CarbonComputers/Hackberry-Pi-CM5/RTC-Battery/README.md

# RTC_Battery on HackberryPi_CM5

There is an RTC battery on board on HackberryPi_CM5 and is pre-installed before delivery



You can check the battery voltage first by typing this in terminal:

```sh
cat /sys/devices/platform/soc/soc:rpi_rtc/rtc/rtc0/battery_voltage
```


A new battery voltage should be around 3.3V, so it read should be approximately 3300000
