CarbonComputers/Hackberry-Pi-CM5/Compatible OS/LineageOS/Readme.md

# Install LineageOS on HackberryPi_CM5

### LineageOS is an open source Android operating system for smartphones, tablets, and set-top boxes. It is community-developed and serves as the successor to [CyanogenMod](https://en.wikipedia.org/wiki/CyanogenMod). The raspberrypi version is developed by konstakang[https://konstakang.com/]. In this OS you can have the Android Blackberry experience on HackberryPi!

```Step1``` Download the Release Image for HackberryPi_CM5 on this [page]  
```Step2``` Flash the downloaded image into a TF card   
```Step3``` Insert the TF card into the HackberryPi_CM5 and power it on, wait a few seconds and you can see it booting
