CarbonComputers/Hackberry-Pi-CM5/Compatible OS/RaspberryPi_OS/README.md

# Install RaspberryPi OS on HackberryPi_CM5

### RaspberryPi OS has the most support among other OS for different RaspberryPi SBCs, it is recommended to install RaspberryPi OS on HackberryPi_CM5
