CarbonComputers/Hackberry-Pi-CM5/Compatible OS/Other Projects - OS - Tools/Turn HackberryPi into a music streammer/README.md

https://www.headphonesty.com/2021/04/how-to-build-raspberry-pi-network-music-streamer-with-touchscreen/
