CarbonComputers/Hackberry-Pi-CM5/Compatible OS/Other Projects - OS - Tools/Turn HackberryPi into a NAS/README.md

https://www.pcmag.com/how-to/how-to-turn-a-raspberry-pi-into-a-nas-for-whole-home-file-sharing
