CarbonComputers/Hackberry-Pi-CM5/3D-Model/CyberPunk Case/HP CM5 Cyberpunk Orange.jpg

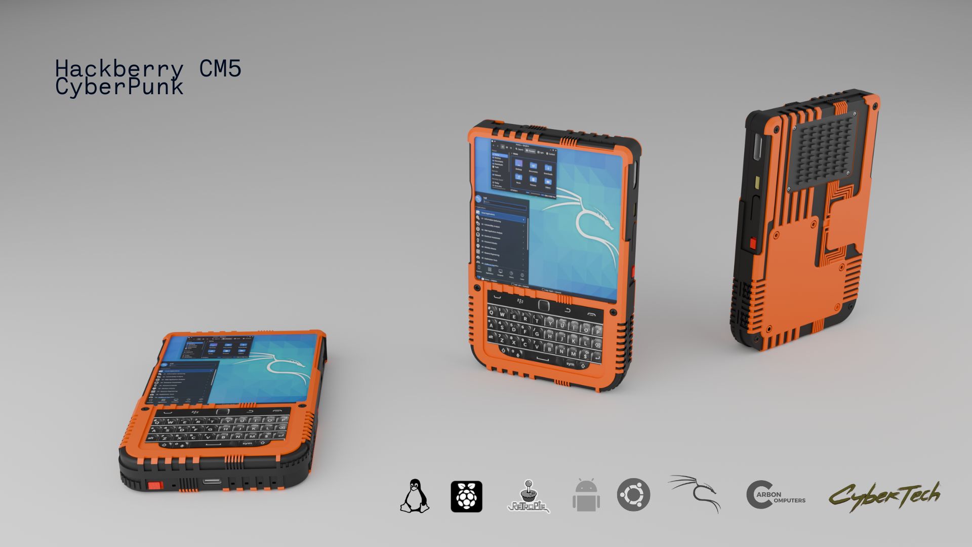
3D-Model/CyberPunk Case/HP CM5 Cyberpunk Orange.jpg
