CarbonComputers/Hackberry-Pi-CM5/3D-Model/Explosion.png

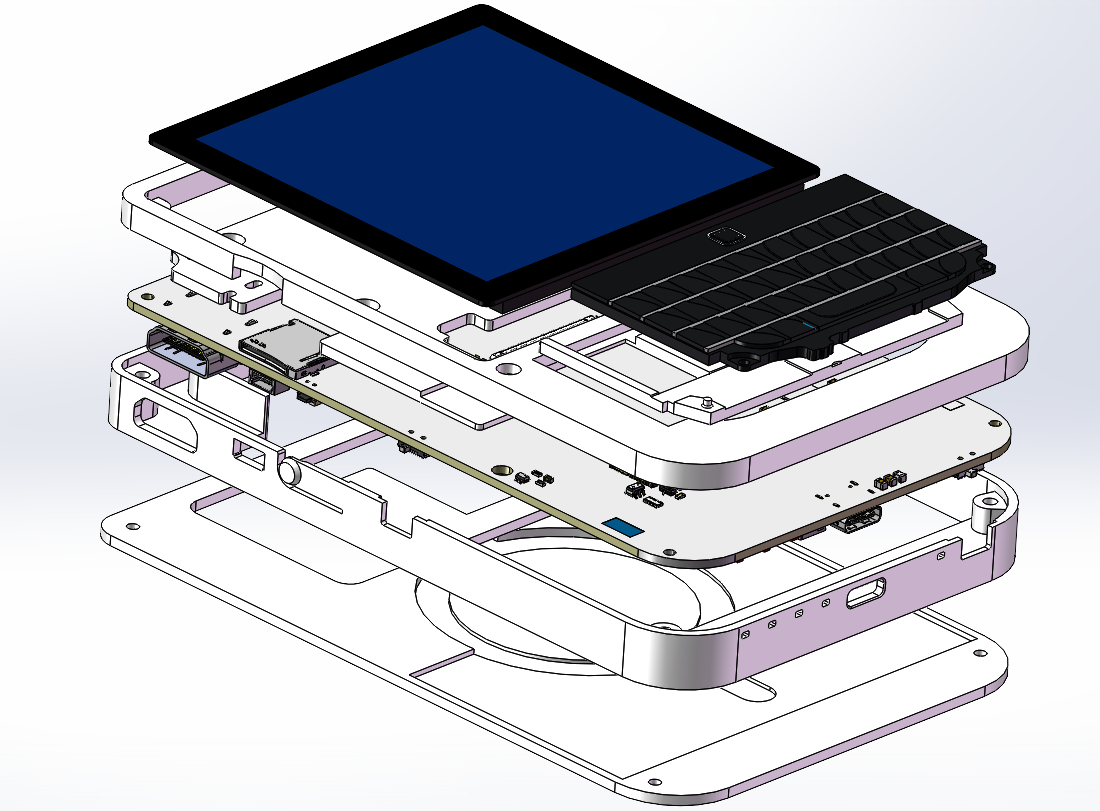
3D-Model/Explosion.png
