CarbonComputers/Hackberry-Pi-CM5/M.2 SATA NVME Slot/Format.png

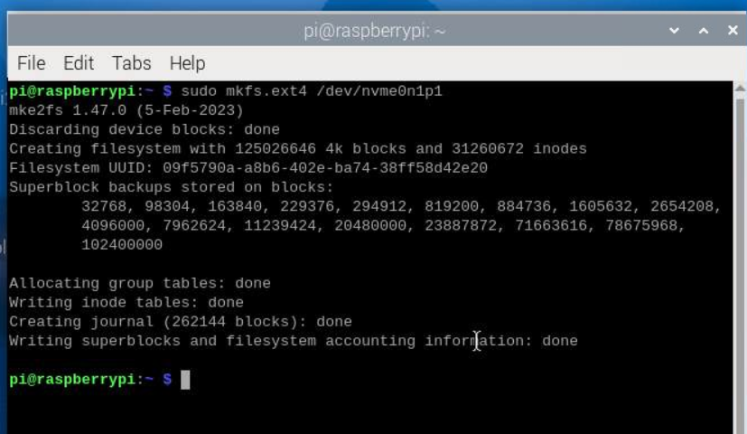
M.2 SATA NVME Slot/Format.png
