CarbonComputers/Hackberry-Pi-CM5/M.2 SATA NVME Slot/New Partition.png

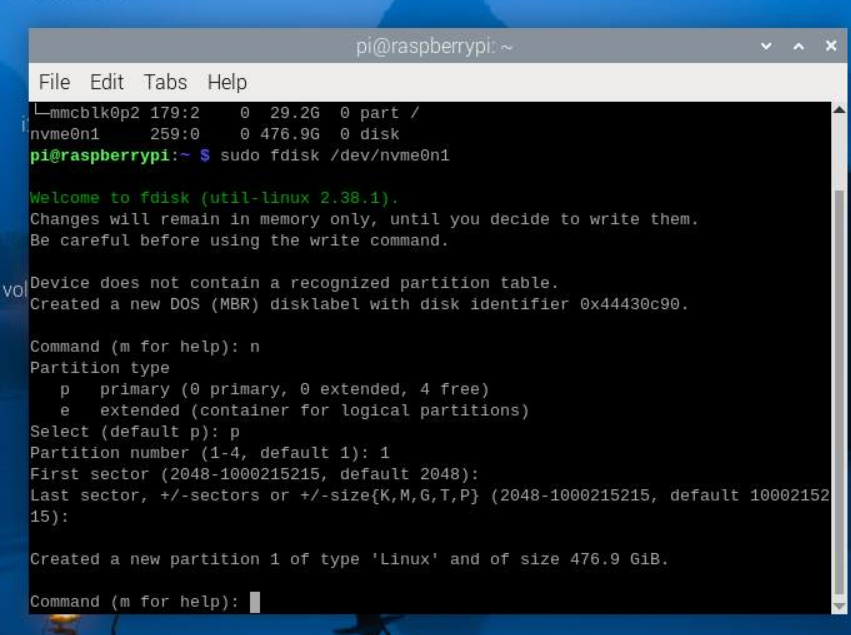
M.2 SATA NVME Slot/New Partition.png
