CarbonComputers/Hackberry-Pi-CM5/M.2 SATA NVME Slot/SD card copier.png

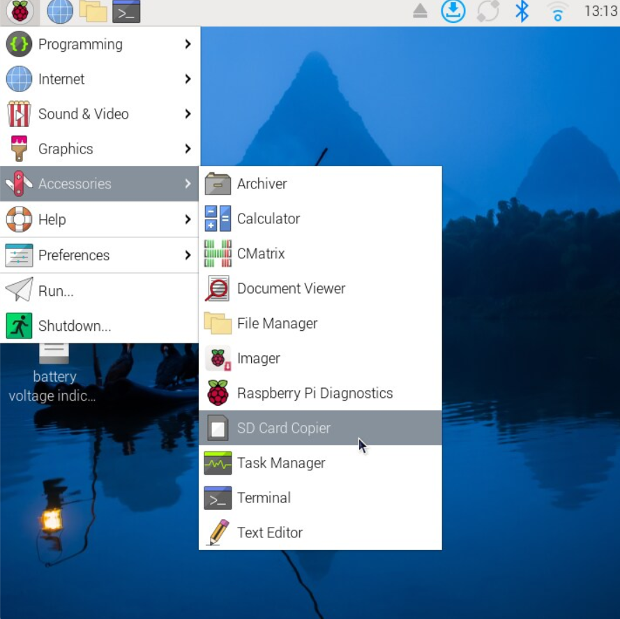
M.2 SATA NVME Slot/SD card copier.png
