CarbonComputers/Hackberry-Pi-CM5/Speakers/Speaker-Layout.png

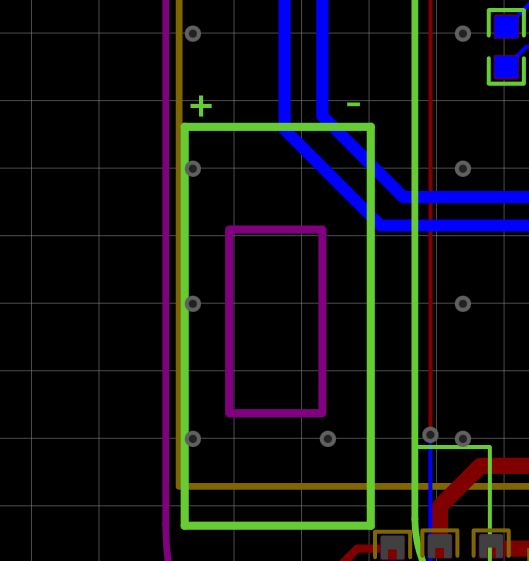
Speakers/Speaker-Layout.png
