CarbonComputers/Hackberry-Pi-CM5/Speakers/Speaker_Circuit.png

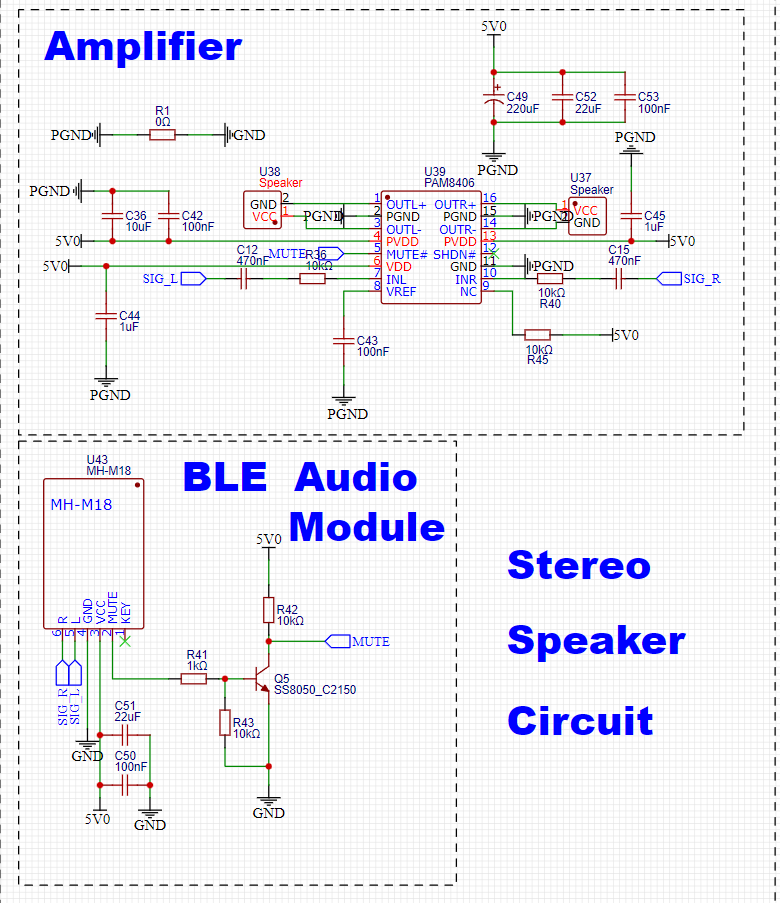
Speakers/Speaker_Circuit.png
