CarbonComputers/Hackberry-Pi-CM5/3D-Model/HackberryPi_CM5_White_Screwtool.STL

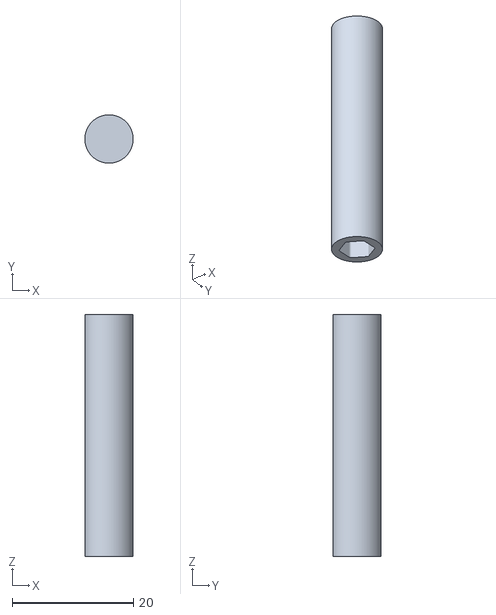
[picture p32: CAD file, 2025-05-13]
3D-Model/HackberryPi_CM5_White_Screwtool.STL
8.00 x 8.00 x 40.0
