CarbonComputers/Hackberry-Pi-CM5/M.2 SATA NVME Slot/ReadWrite Test.png

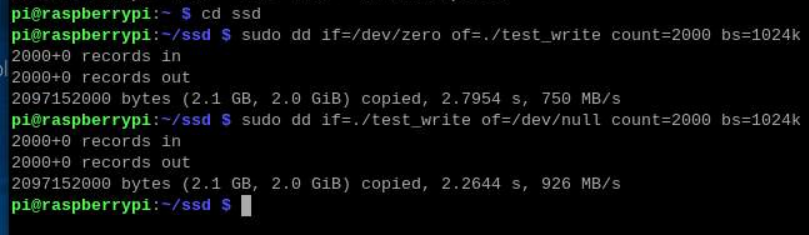
M.2 SATA NVME Slot/ReadWrite Test.png
